glowingkitty/GlowPrinter/3D printed parts/corner connectors/back top left outside.3mf

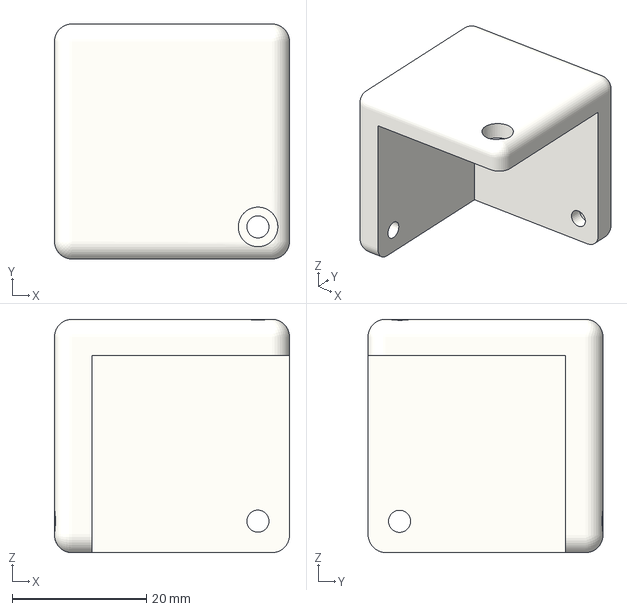
[picture p20: CAD file, 2021-10-13]
3D printed parts/corner connectors/back top left outside.3mf
35.0 x 35.0 x 34.8 mm
