glowingkitty/GlowPrinter/3D printed parts/corner connectors/back bottom left outside.3mf

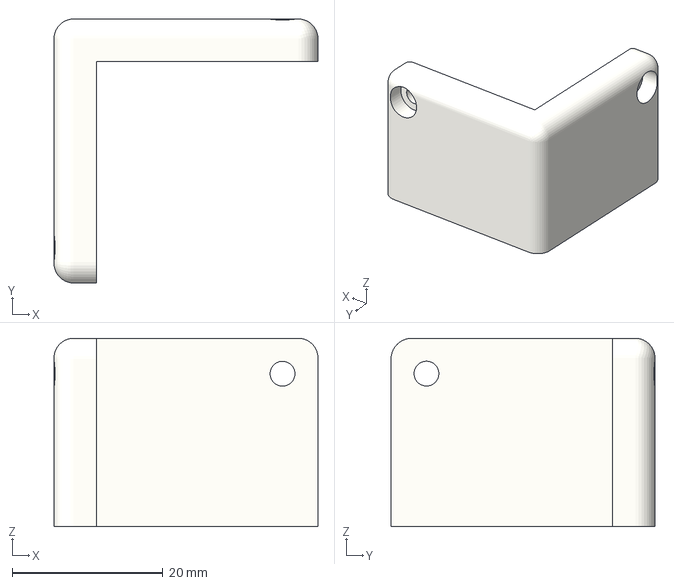
[picture p21: CAD file, 2021-10-13]
3D printed parts/corner connectors/back bottom left outside.3mf
35.0 x 35.0 x 25.0 mm
