glowingkitty/GlowPrinter/3D printed parts/corner connectors/back bottom right outside.3mf

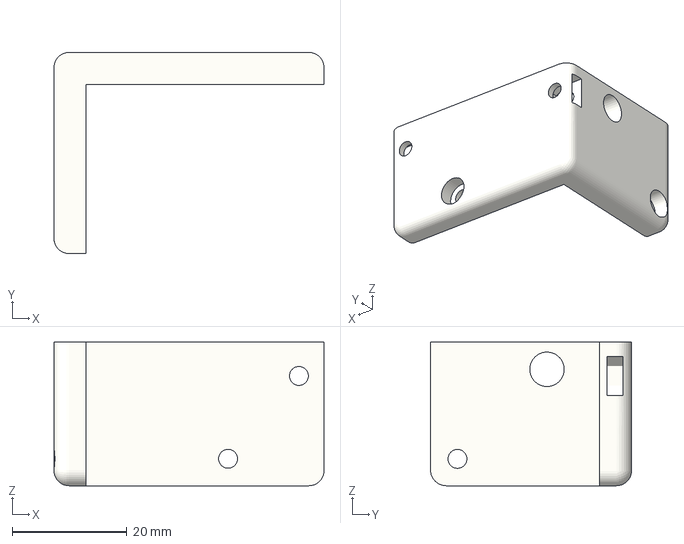
[picture p22: CAD file, 2021-10-13]
3D printed parts/corner connectors/back bottom right outside.3mf
47.0 x 35.0 x 25.0 mm
